idiot-io/candy/hardware/releases/panel-threeCandy-double-26062018.png

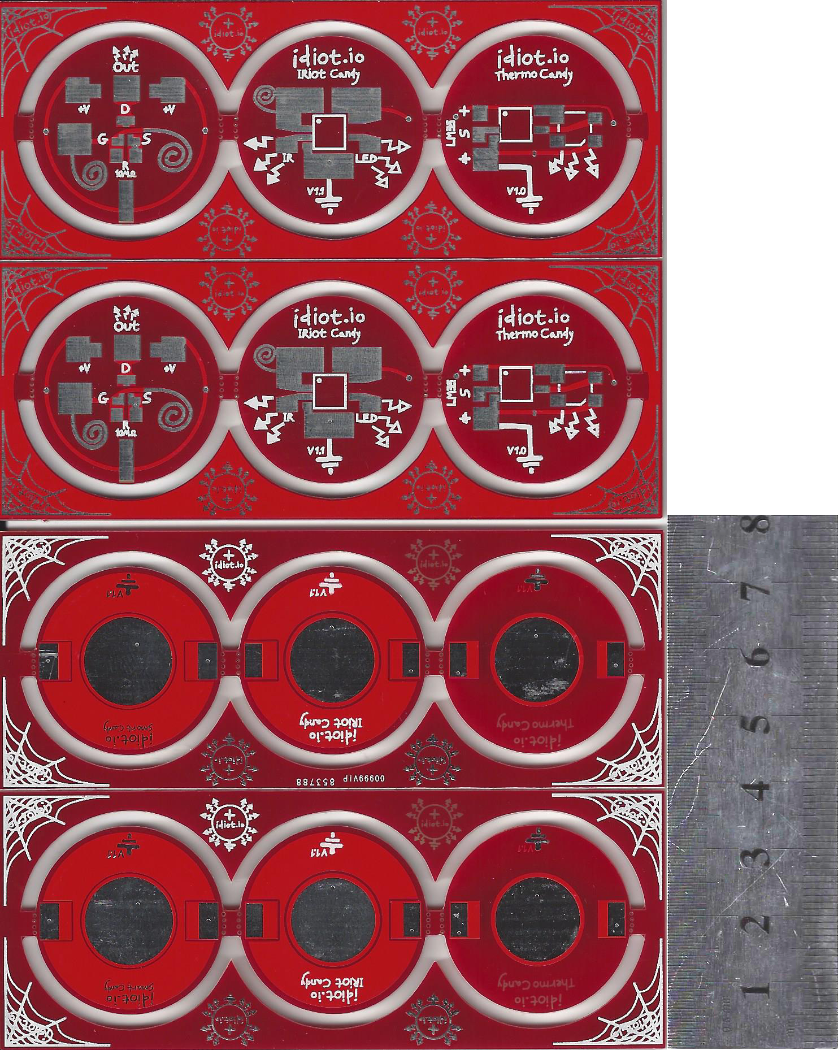
hardware/releases/panel-threeCandy-double-26062018.png
