idiot-io/candy/hardware/releases/panel-threeCandy-double-27062018.png

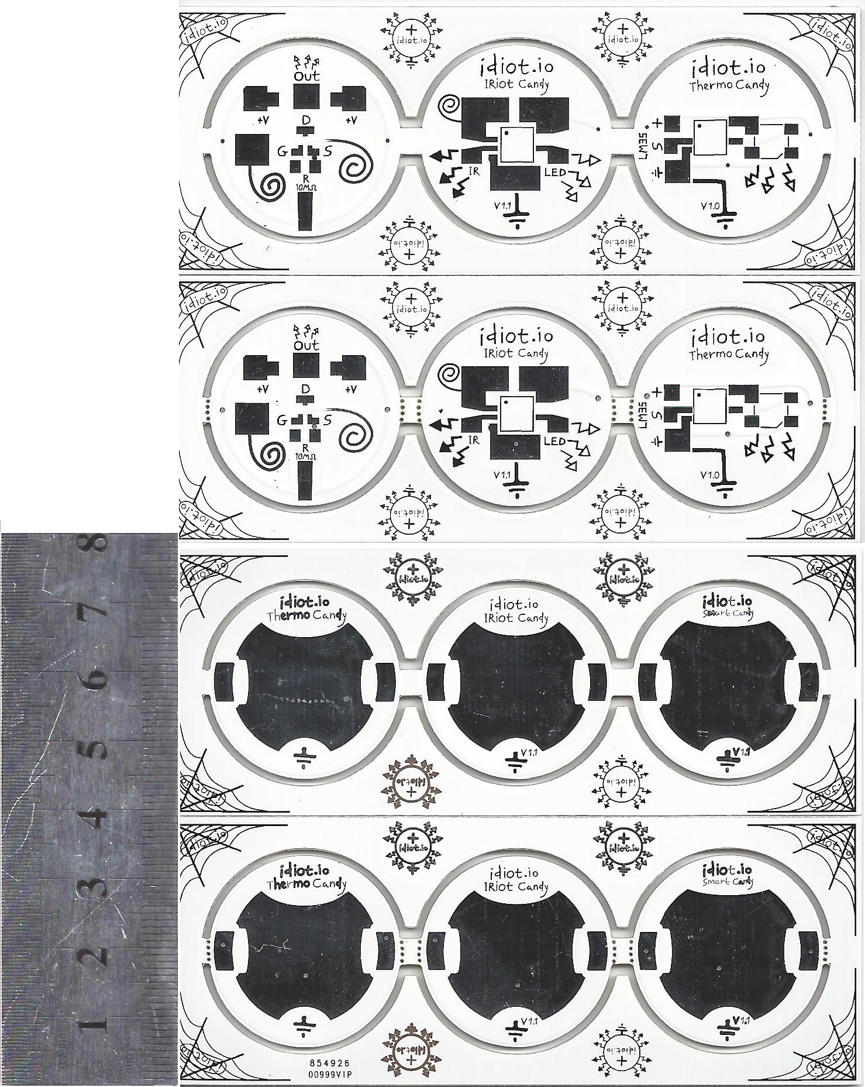
hardware/releases/panel-threeCandy-double-27062018.png
