idiot-io/candy/hardware/releases/panelinkscape.png

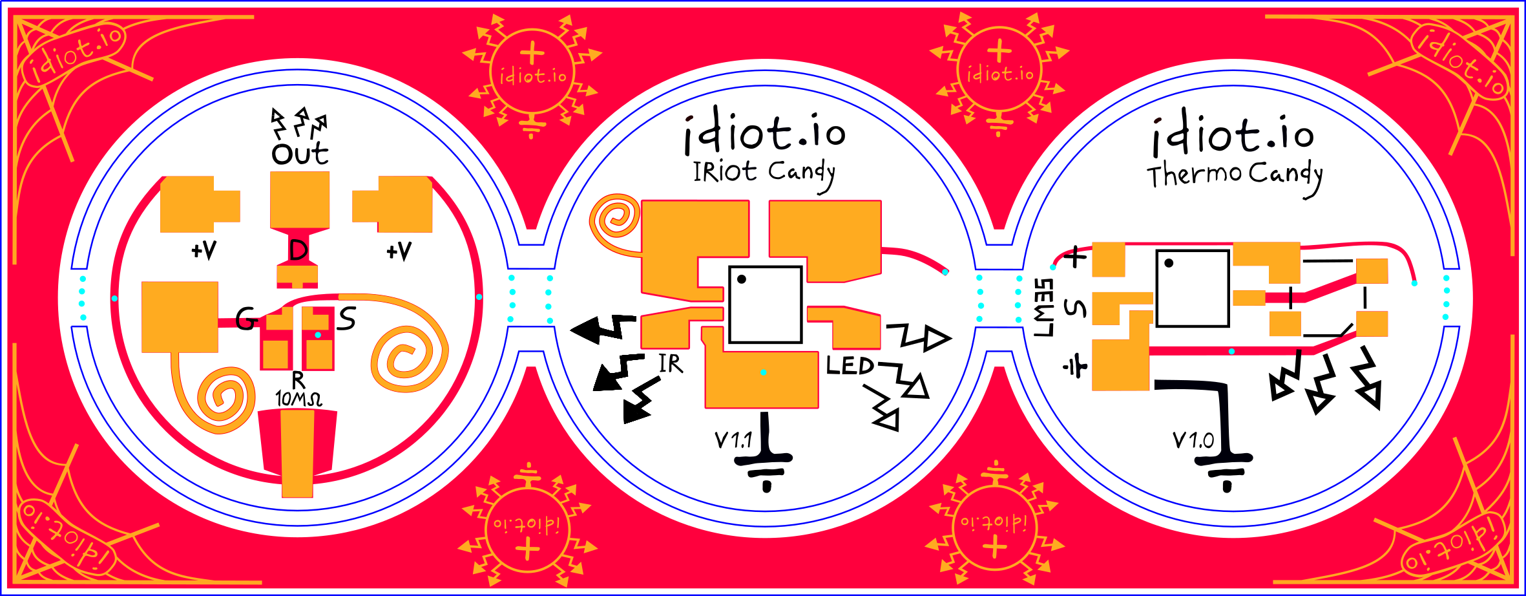
hardware/releases/panelinkscape.png
